Tonikiller10000/ArmonicLevitationDevice/LevitationPictures/41.png

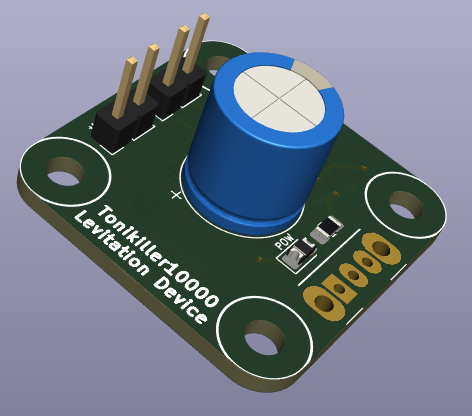
LevitationPictures/41.png
