Tonikiller10000/ArmonicLevitationDevice/LevitationPictures/42.png

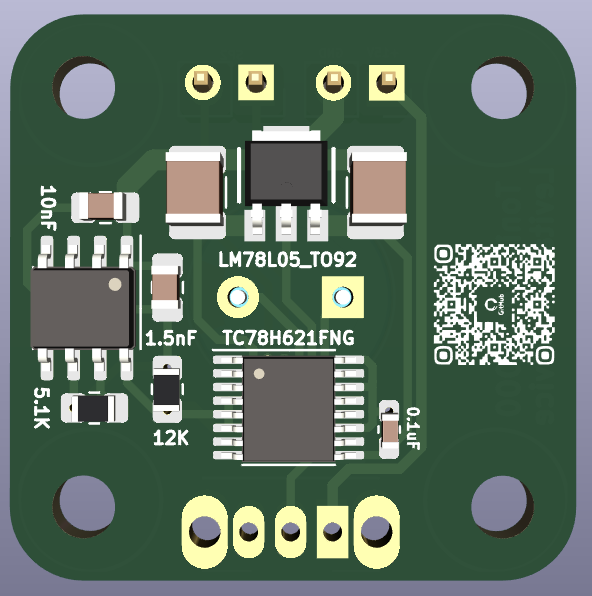
LevitationPictures/42.png
