Tonikiller10000/ArmonicLevitationDevice/LevitationPictures/46.png

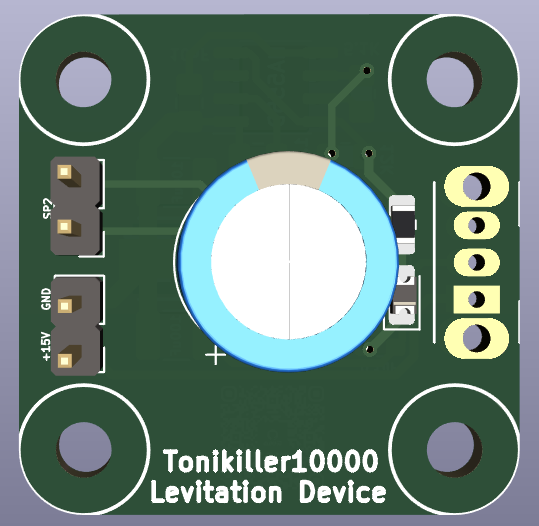
LevitationPictures/46.png
