Tonikiller10000/ArmonicLevitationDevice/LevitationPictures/20231217_032505.jpg

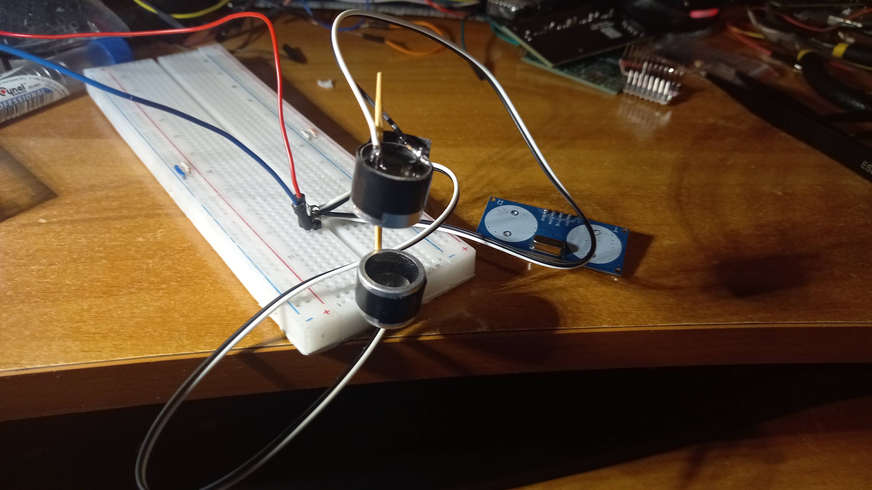
LevitationPictures/20231217_032505.jpg
