Tonikiller10000/ArmonicLevitationDevice/LevitationPictures/20231217_032524.jpg

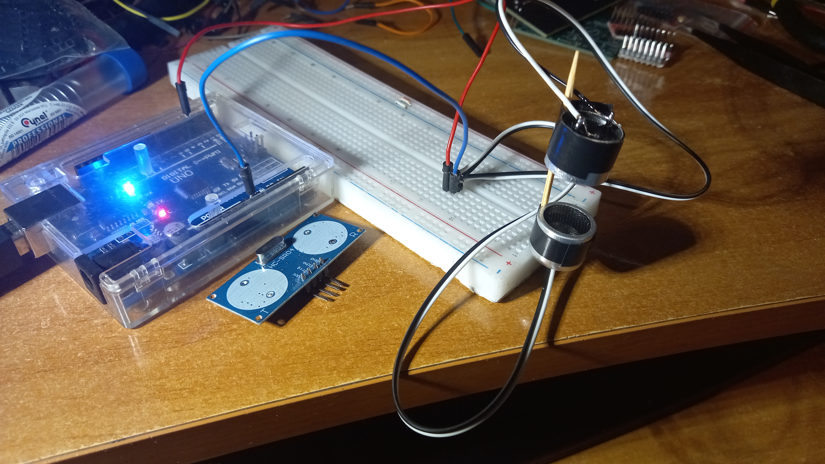
LevitationPictures/20231217_032524.jpg
