Tonikiller10000/ArmonicLevitationDevice/LevitationPictures/PCB.png

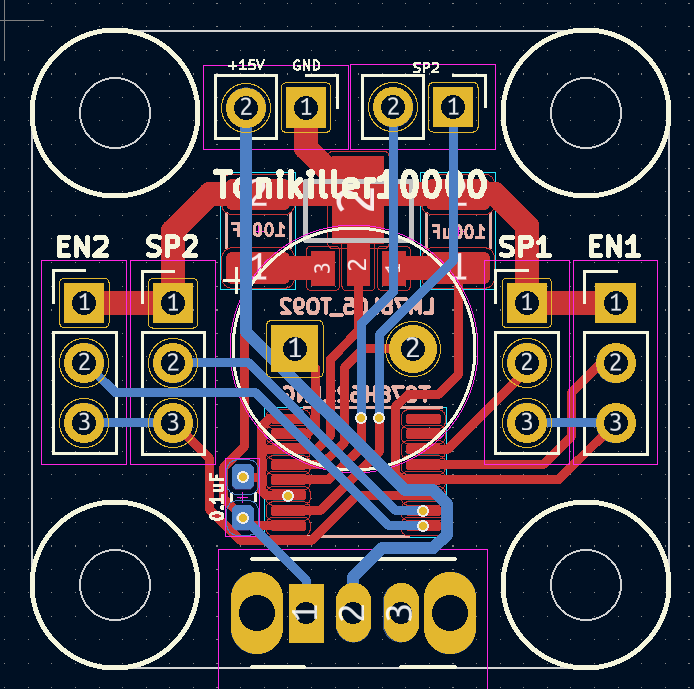
LevitationPictures/PCB.png
