Tonikiller10000/ArmonicLevitationDevice/LevitationPictures/{36DB49B8-093F-47D0-9F32-C4C974DCAD02}.png

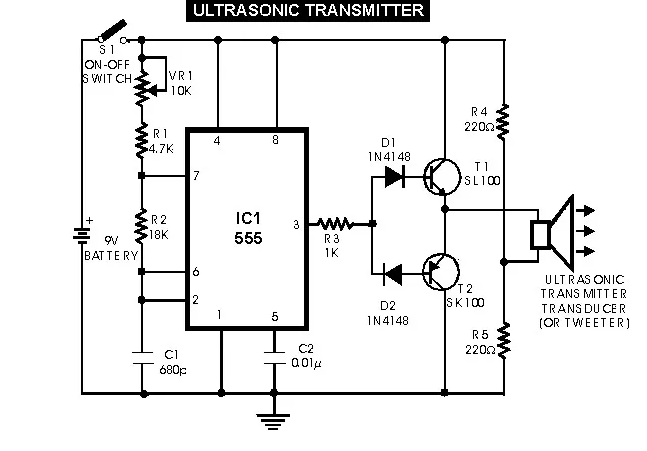
LevitationPictures/{36DB49B8-093F-47D0-9F32-C4C974DCAD02}.png
